issalig/galaksija/hw/galaksija_keyb_pcb.pdf

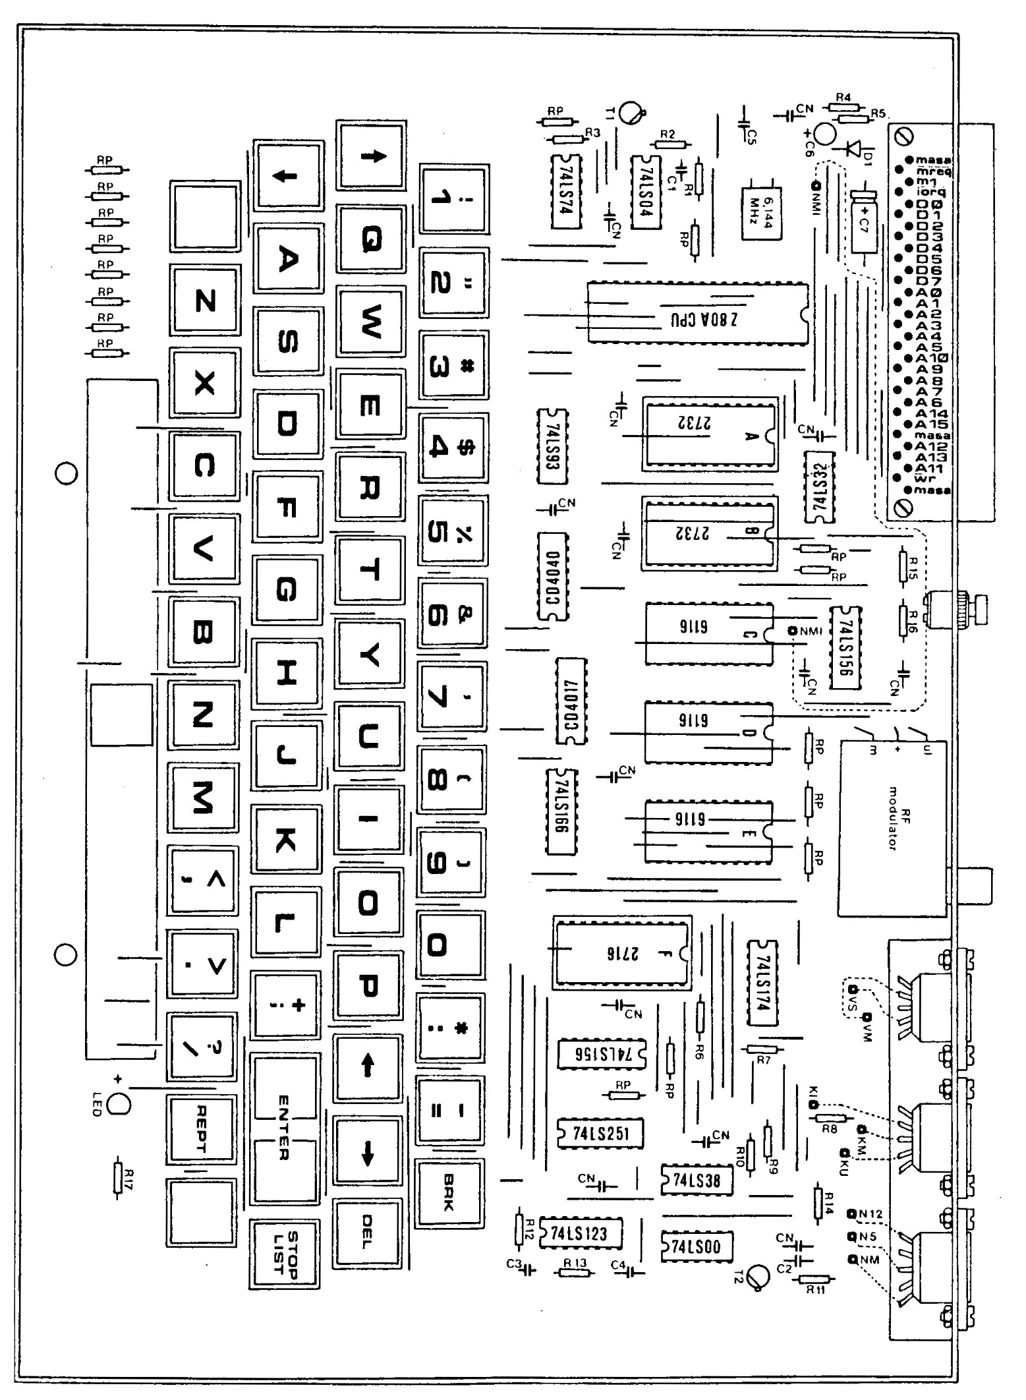
[picture p7: page 1]
