issalig/galaksija/hw/galaksija_sch.pdf

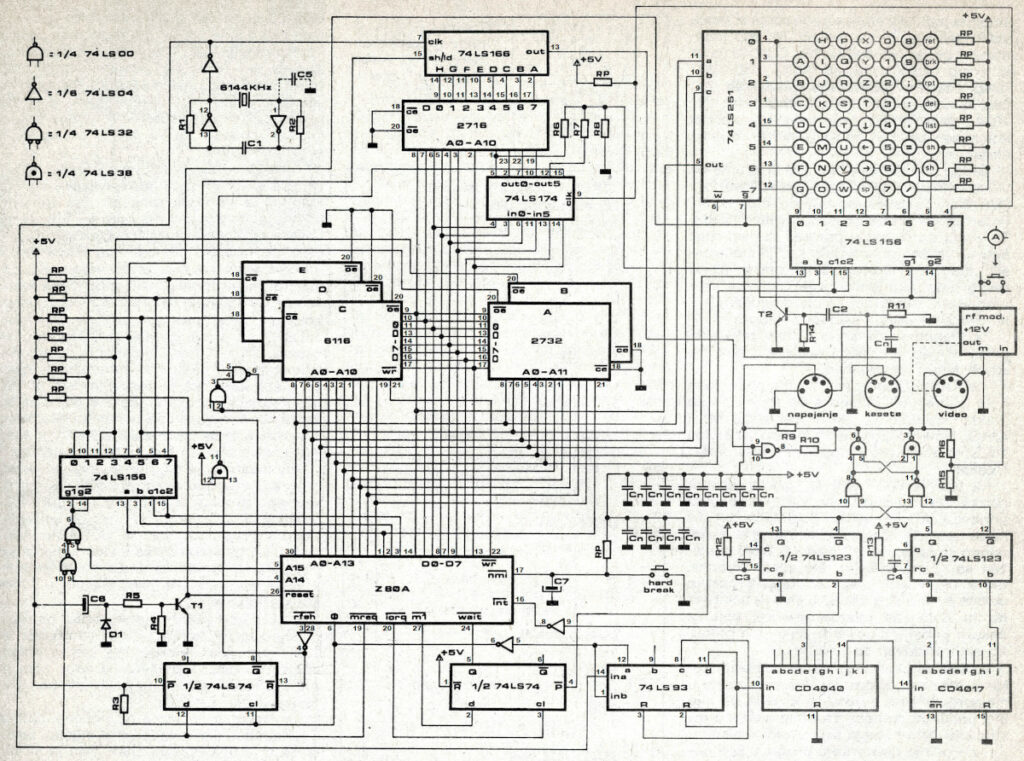
[picture p8: page 1]
