issalig/galaksija/case/galaksija_case_base_4.stl

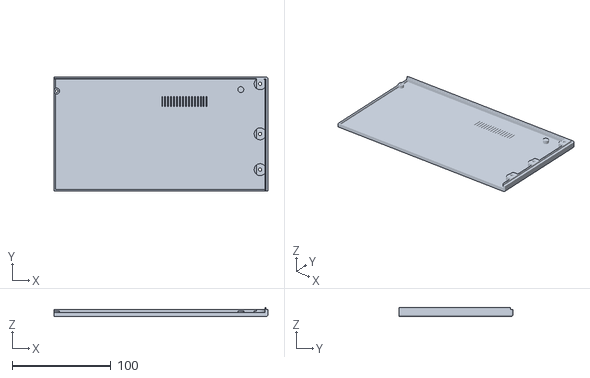
[picture p28: CAD file, 2025-02-05]
case/galaksija_case_base_4.stl
216.7 x 115.6 x 8.99
