issalig/galaksija/case/misc/logo.stl

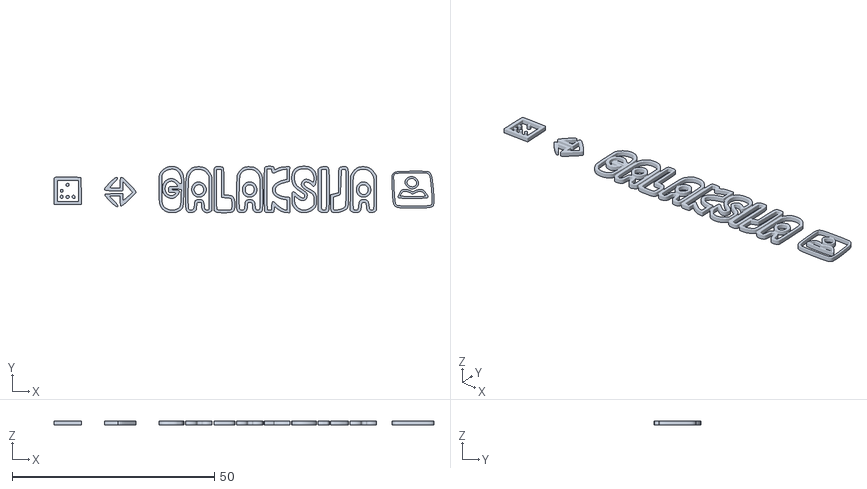
[picture p29: CAD file, 2025-02-05]
case/misc/logo.stl
94.0 x 11.5 x 1.00
