issalig/galaksija/case/galaksija_case_top_1.stl

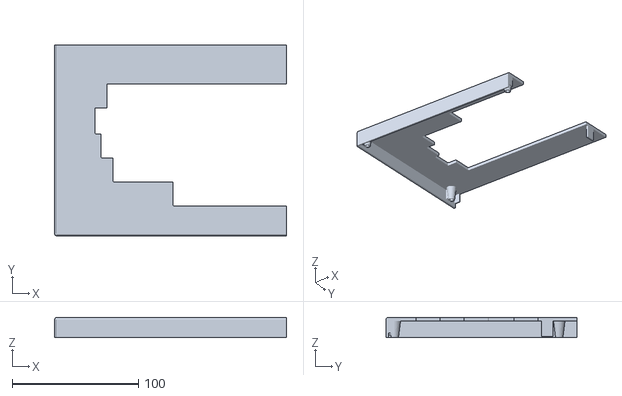
[picture p30: CAD file, 2025-02-05]
case/galaksija_case_top_1.stl
183.8 x 151.5 x 16.0
