issalig/galaksija/case/misc/galaksija_logo_plate.stl

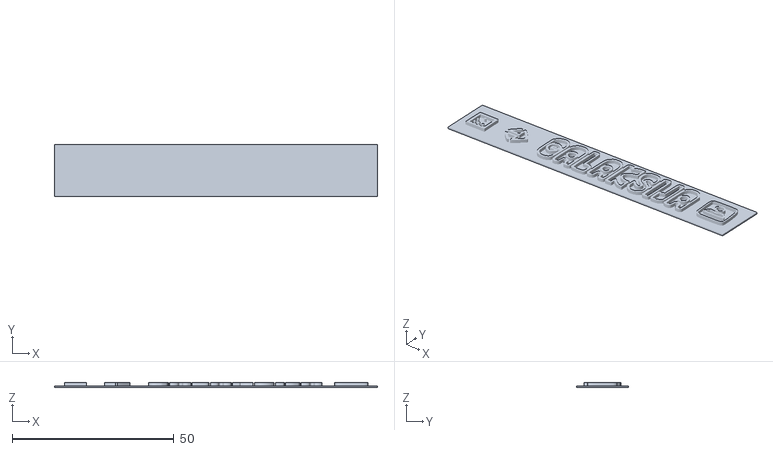
[picture p31: CAD file, 2025-02-05]
case/misc/galaksija_logo_plate.stl
100.0 x 16.0 x 1.50
