issalig/galaksija/case/galaksija_keys.dxf

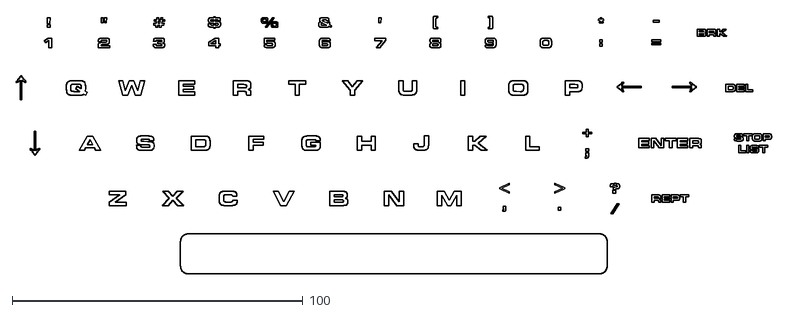
[picture p32: CAD file, 2025-02-04]
case/galaksija_keys.dxf
259.7 x 88.6
