issalig/galaksija/case/galaksija_keys_and_contour.dxf

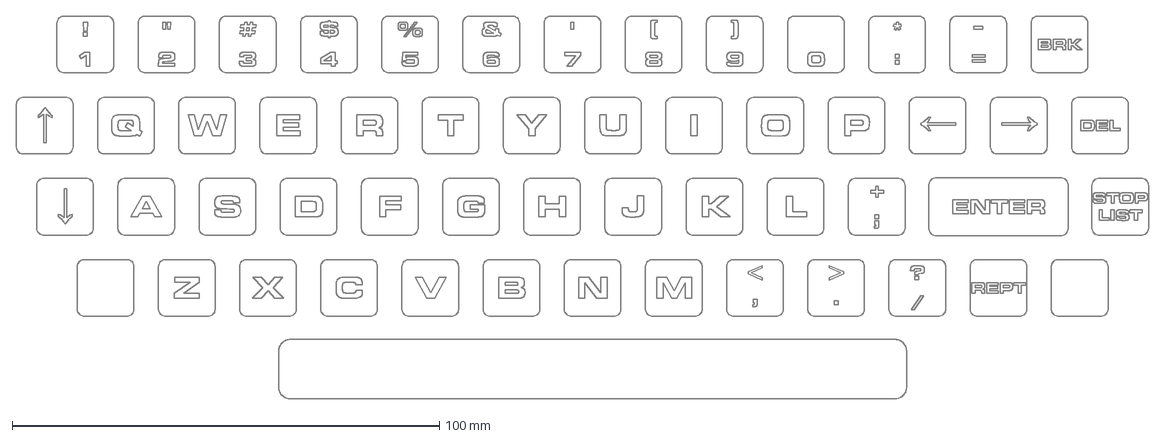
[picture p33: CAD file, 2025-02-04]
case/galaksija_keys_and_contour.dxf
265.0 x 89.6 mm
