issalig/galaksija/case/galaksija_keys_contour.dxf

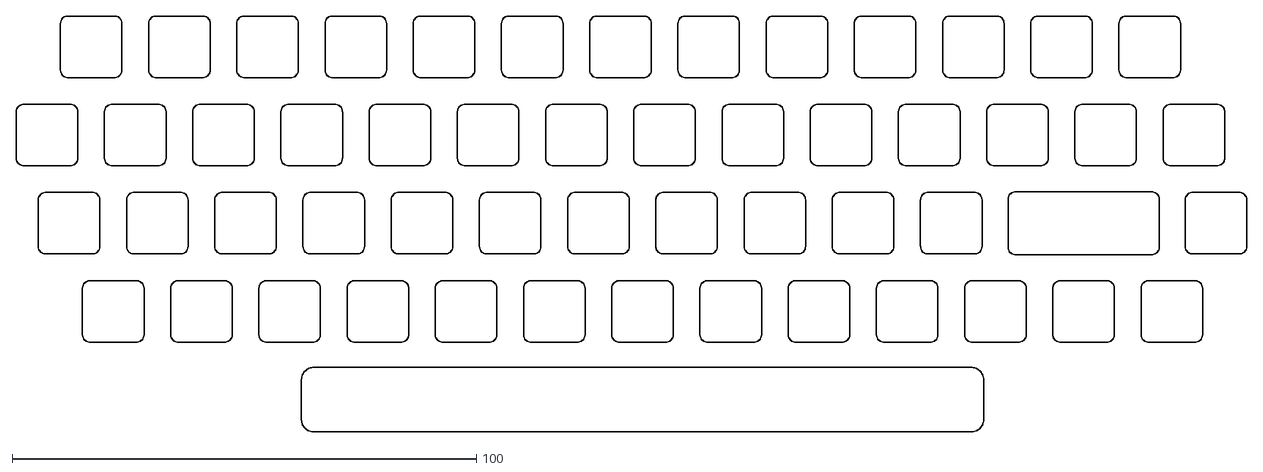
[picture p34: CAD file, 2025-02-04]
case/galaksija_keys_contour.dxf
265.0 x 89.6
